SmallRobot2000/AMIX-68k/code/execs/src/cat/main.c

#include <stdio.h>

void print_file(const char *filename) {
    FILE *file = fopen(filename, "r");
    if (!file) {
        perror(filename);
        return;
    }

    int ch;
    while ((ch = fgetc(file)) != EOF) {
        putchar(ch);
    }

    fclose(file);
}

int main(int argc, char *argv[]) {
    if (argc < 2) {
        fprintf(stderr, "Usage: %s <file1> [file2 ...]\n", argv[0]);
        return 1;
    }

    for (int i = 1; i < argc; i++) {
        print_file(argv[i]);
    }

    return 0;
}
