SmallRobot2000/AMIX-68k/code/C/include/RTC.h

#include <stdint.h>

void rtc_set_time(uint8_t sec, uint8_t min, uint8_t hr, uint8_t day, uint8_t date, uint8_t mon, uint8_t yr);
void rtc_get_time(uint8_t *sec, uint8_t *min, uint8_t *hr, uint8_t *day, uint8_t *date, uint8_t *mon, uint8_t *yr);
uint8_t ds3234_read_register(uint8_t addr);
void rtc_init(void);
