SmallRobot2000/AMIX-68k/code/execs/src/test/main.c

#include<stdio.h>
#include<stdint.h>
extern char **environ;

int main(int argc, char *argv[])
{
    //printf("Im a called task, my args:\nargc: %x\nargv: %p\nenv_ptr = %p\n",argc, argv, environ);
    __asm__("illegal");

    for (int i = 0; ; i++) {
        printf("%s\n", environ[i]);
    }
    return 0;
}
